BenEspinoza10/RescueLineRobotMustakis/Archivos de construccion/V1.1/BaseDynamisV2.dxf

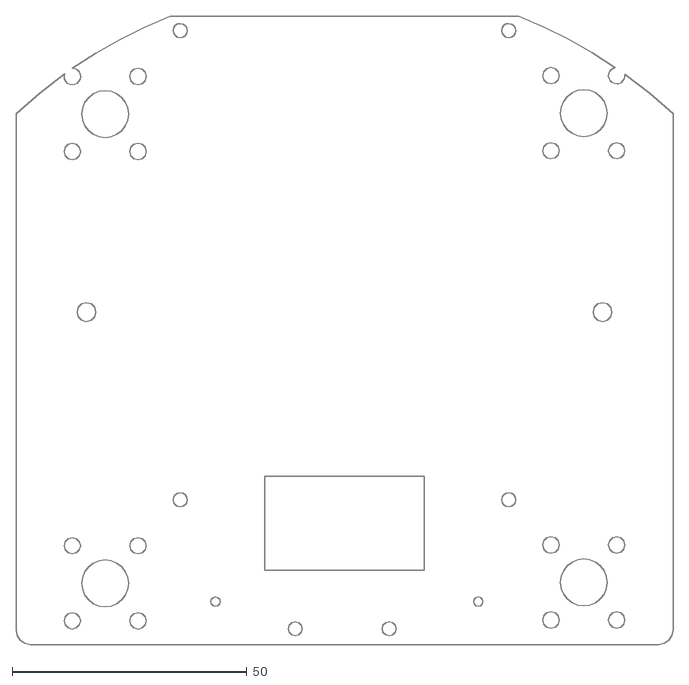
[picture p18: CAD file, 2025-03-11, an earlier design]
Archivos de construccion/V1.1/BaseDynamisV2.dxf
140.0 x 133.8
