BenEspinoza10/RescueLineRobotMustakis/Pruebas/SensorRGB/SensorRGB.ino

#include "Wire.h"
#include "Adafruit_TCS34725.h"
/*
  Connect SCL to analog 5
  Connect SDA to analog 4
  Connect VDD to 3.3V DC
  Connect GROUND to common ground */

/* Initialise with default values (int time = 2.4ms, gain = 1x) */
 Adafruit_TCS34725 tcs = Adafruit_TCS34725(100,TCS34725_GAIN_1X);

/* Initialise with specific int time and gain values */
//Adafruit_TCS34725 tcs = Adafruit_TCS34725(TCS34725_INTEGRATIONTIME_700MS, TCS34725_GAIN_1X);

void setup(void) {
  Serial.begin(115200);

  if (tcs.begin()) {
    Serial.println("Found sensor");
  } else {
    Serial.println("No TCS34725 found ... check your connections");
    while (1);
  }
}

void loop(void) {
  uint16_t r, g, b, c, colorTemp, lux;

  tcs.getRawData(&r, &g, &b, &c);
  colorTemp = tcs.calculateColorTemperature(r, g, b);
  lux = tcs.calculateLux(r, g, b);

  Serial.print("Color Temp: "); Serial.print(colorTemp);
  Serial.print(" K - ");
  Serial.print("Lux: "); Serial.print(lux); Serial.print(" - ");
  Serial.print("R: "); Serial.print(r); Serial.print(" ");
  Serial.print("G: "); Serial.print(g); Serial.print(" ");
  Serial.print("B: "); Serial.print(b); Serial.print(" ");
  Serial.print("C: "); Serial.print(c); Serial.print(" ");
  Serial.println(" ");
}
